GeneralMine/Wetterstation/Fritzing/Alles_Schaltplan.png

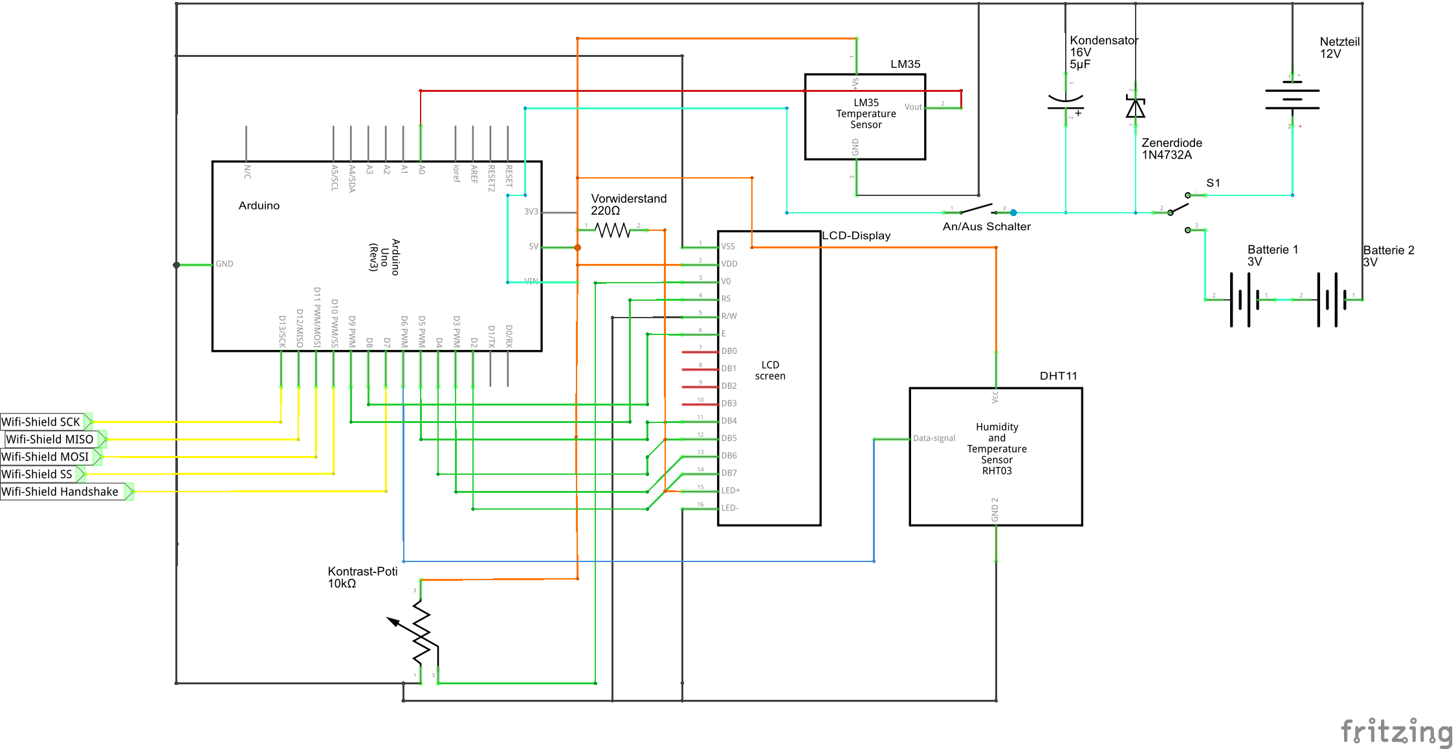
Fritzing/Alles_Schaltplan.png
