GeneralMine/Wetterstation/Medien/20160111_123831.jpg

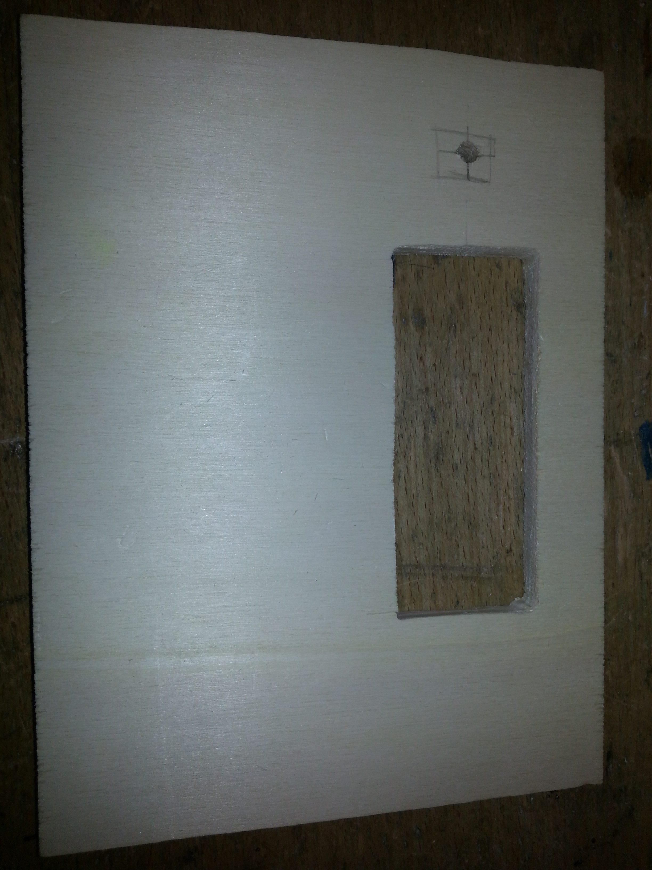
Medien/20160111_123831.jpg
