GeneralMine/Wetterstation/Medien/20160111_123935.jpg

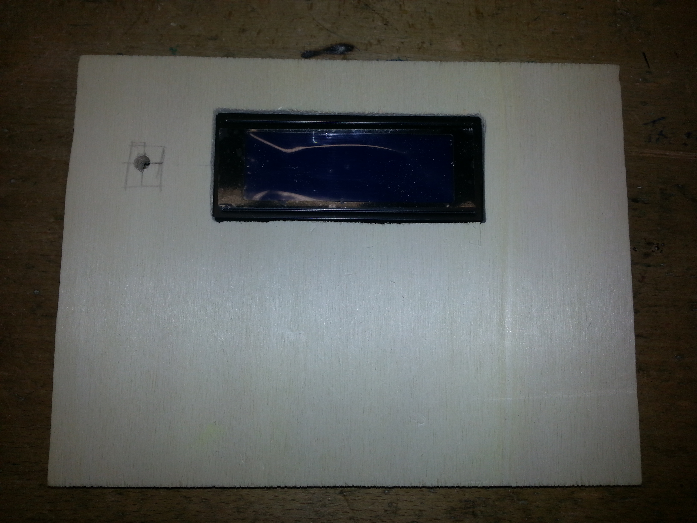
Medien/20160111_123935.jpg
