GeneralMine/Wetterstation/Medien/20160201_120405.jpg

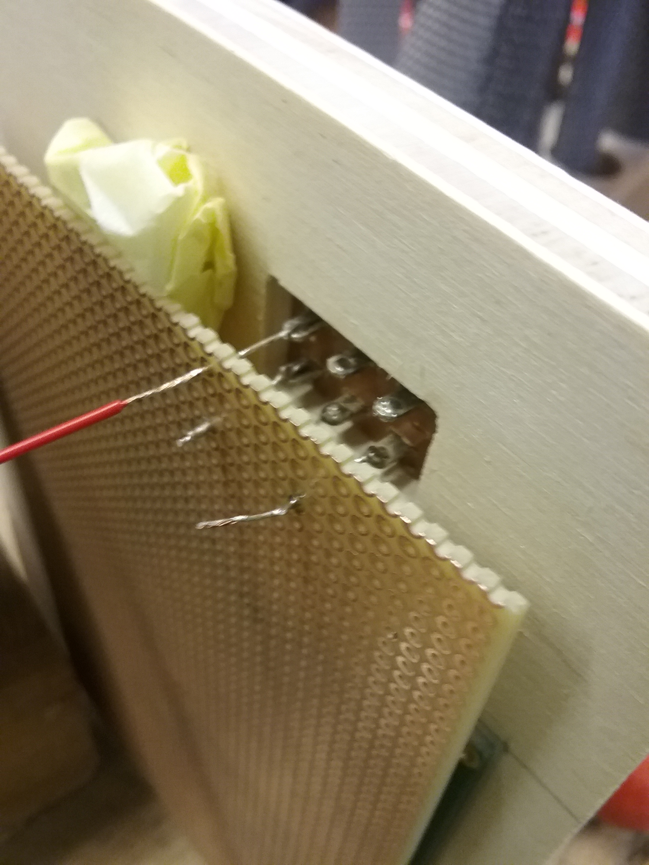
Medien/20160201_120405.jpg
