GeneralMine/Wetterstation/Medien/20160201_120416.jpg

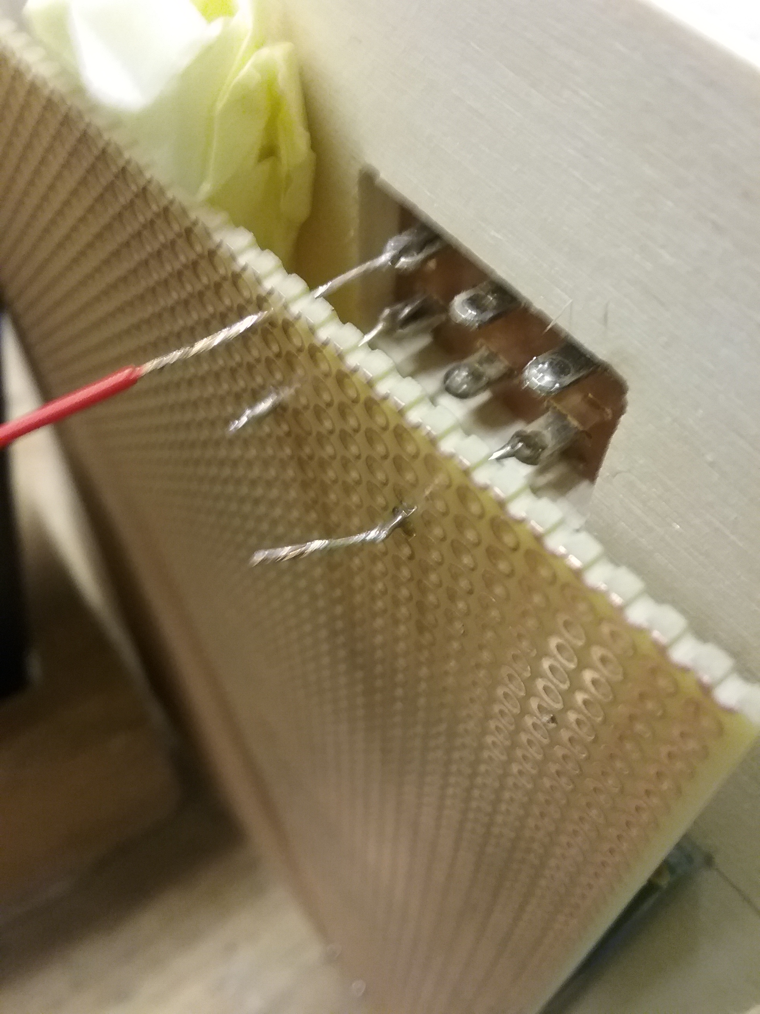
Medien/20160201_120416.jpg
