GeneralMine/Wetterstation/Medien/20160201_124902.jpg

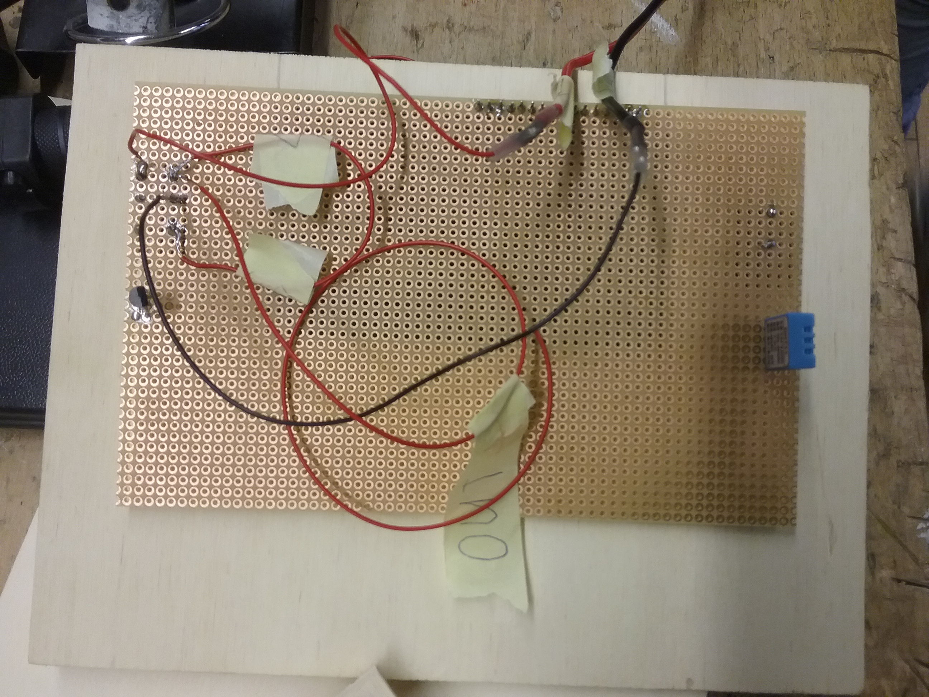
Medien/20160201_124902.jpg
