GeneralMine/Wetterstation/Medien/20160211_163818.jpg

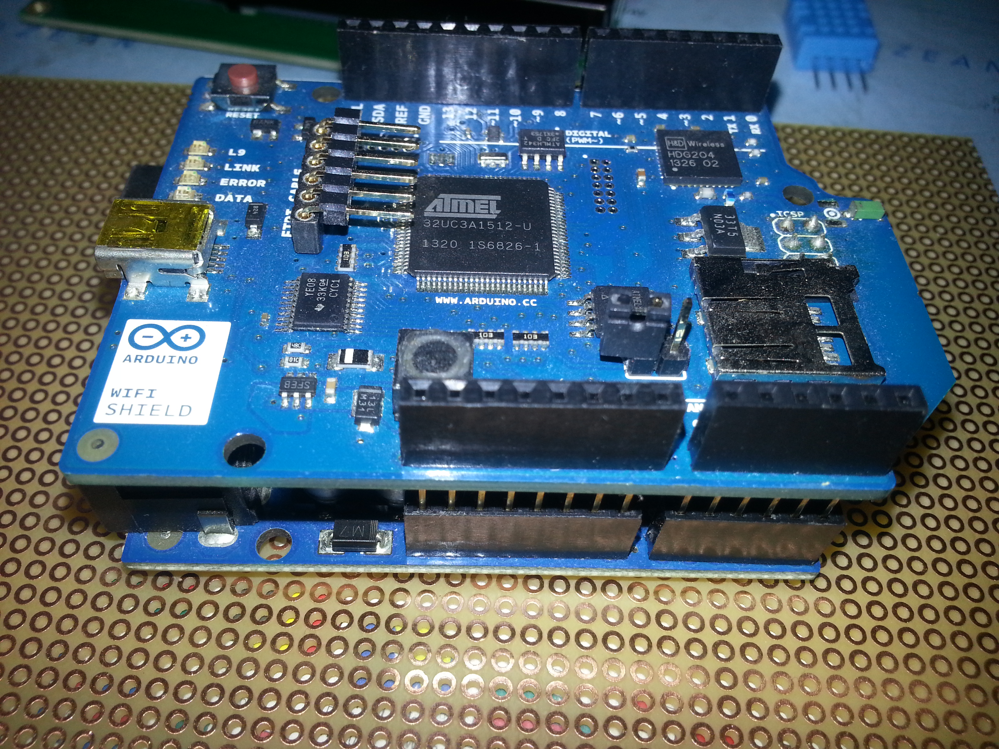
Medien/20160211_163818.jpg
