GeneralMine/Wetterstation/Medien/20160211_163850.jpg

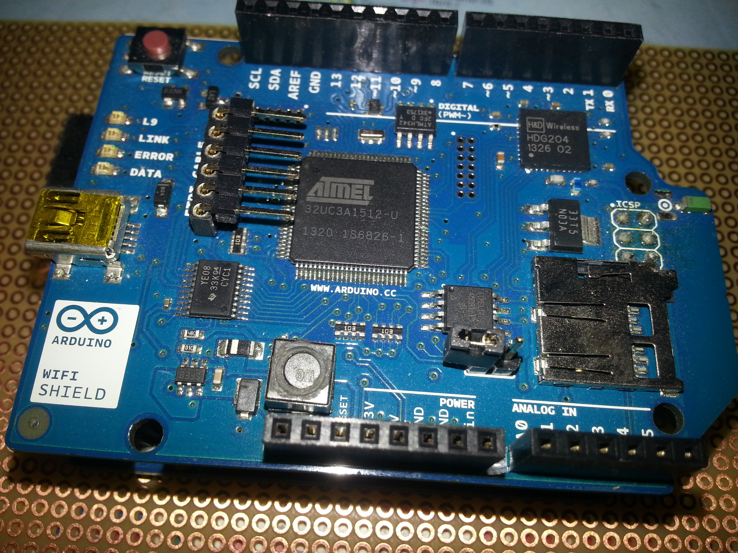
Medien/20160211_163850.jpg
