GeneralMine/Wetterstation/Medien/20160211_163903.jpg

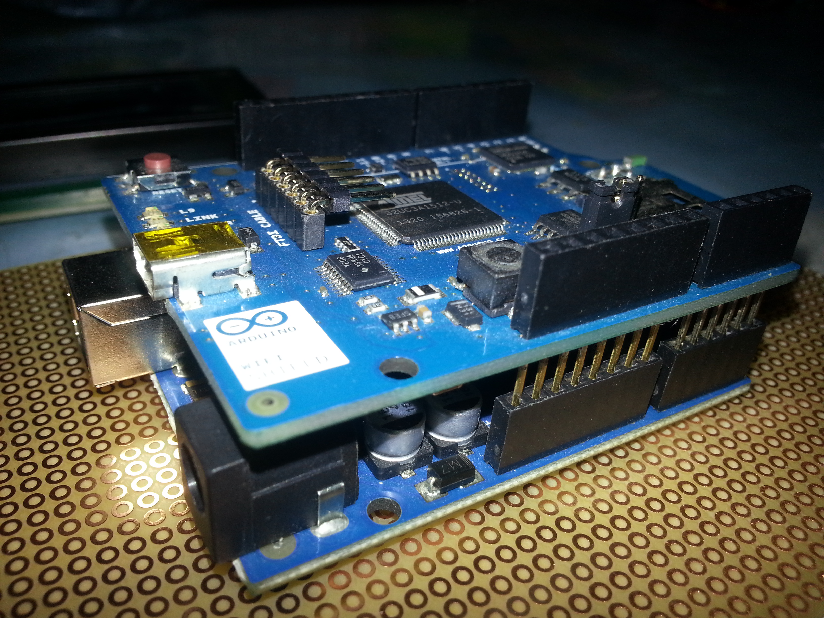
Medien/20160211_163903.jpg
