GeneralMine/Wetterstation/Medien/20160211_163923.jpg

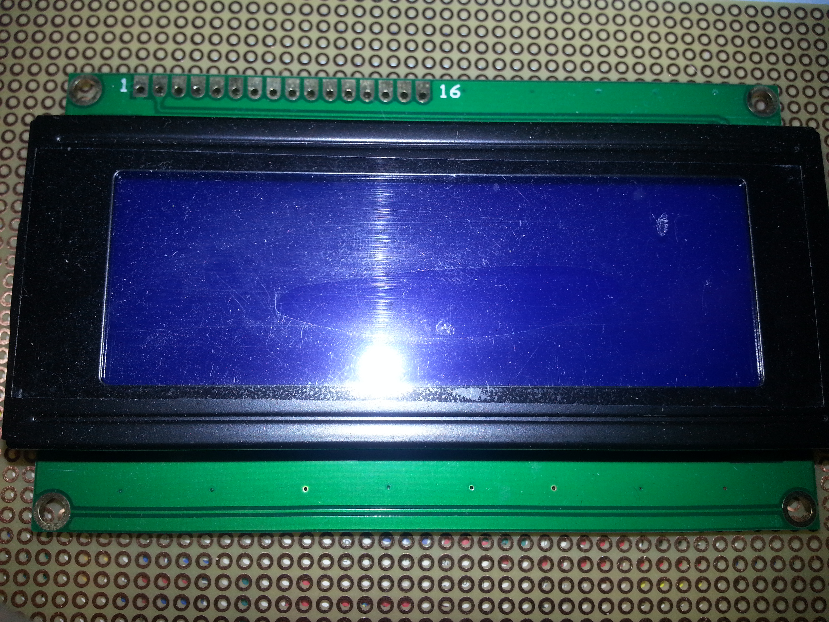
Medien/20160211_163923.jpg
