GeneralMine/Wetterstation/Medien/20160211_163938.jpg

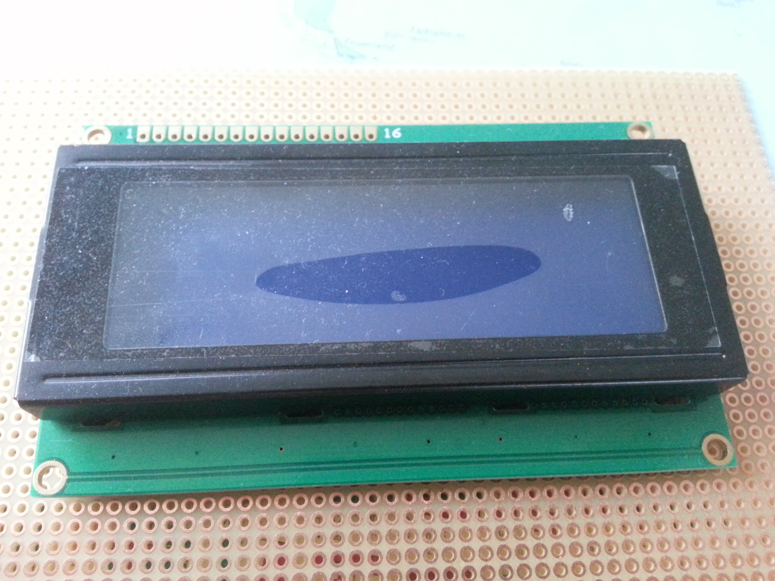
Medien/20160211_163938.jpg
