GeneralMine/Wetterstation/Medien/20160211_163947.jpg

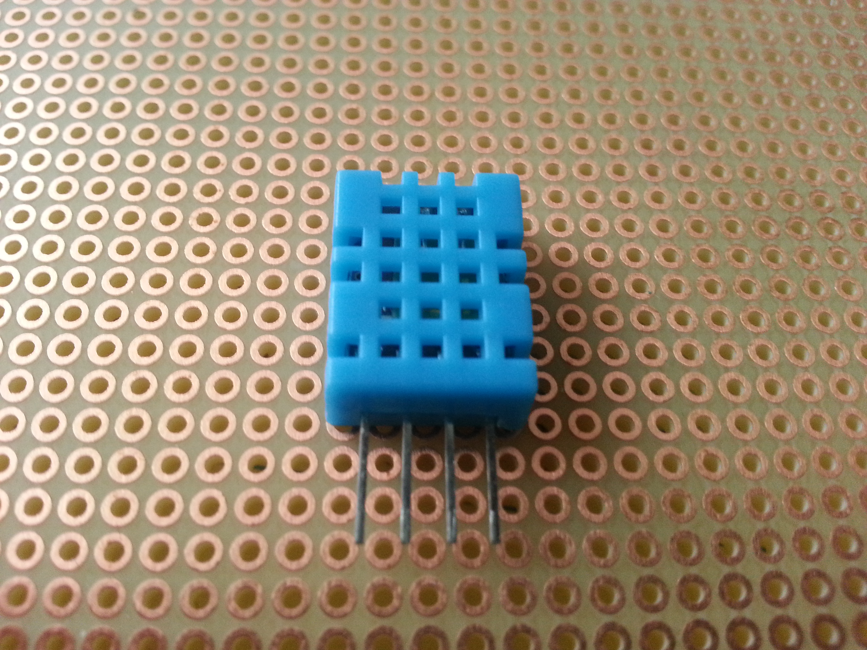
Medien/20160211_163947.jpg
