GeneralMine/Wetterstation/Medien/20160211_164001.jpg

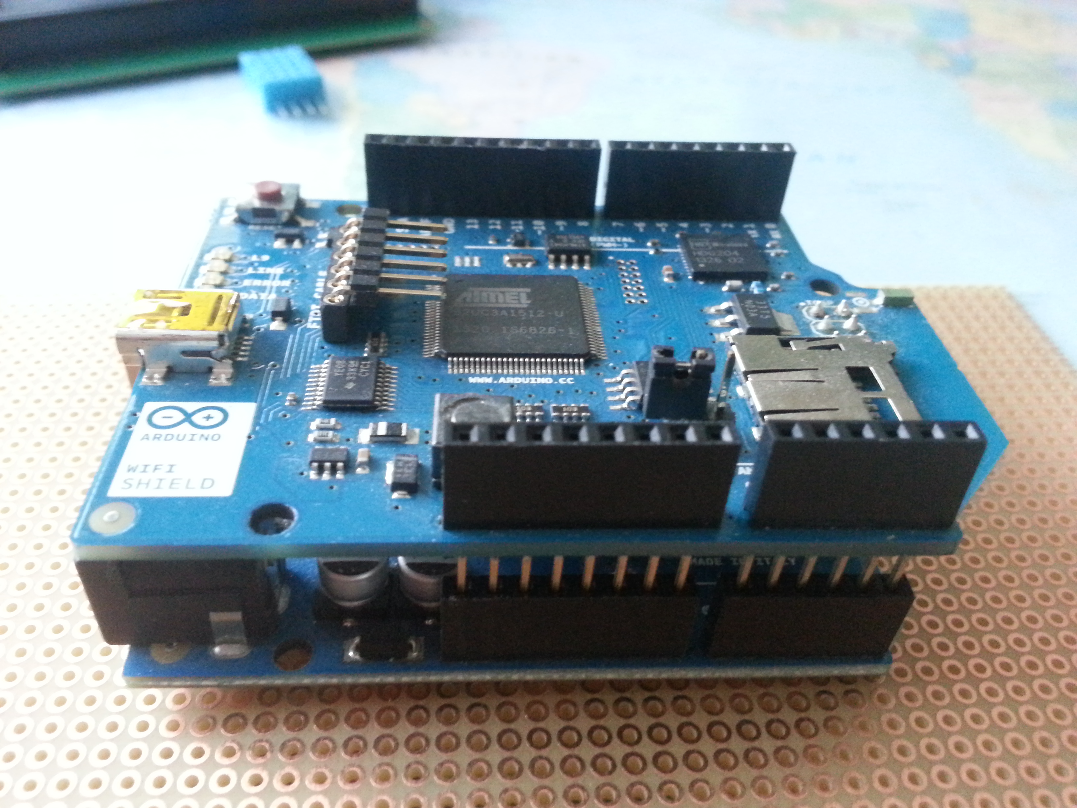
Medien/20160211_164001.jpg
