GeneralMine/Wetterstation/Medien/20160215_125352.jpg

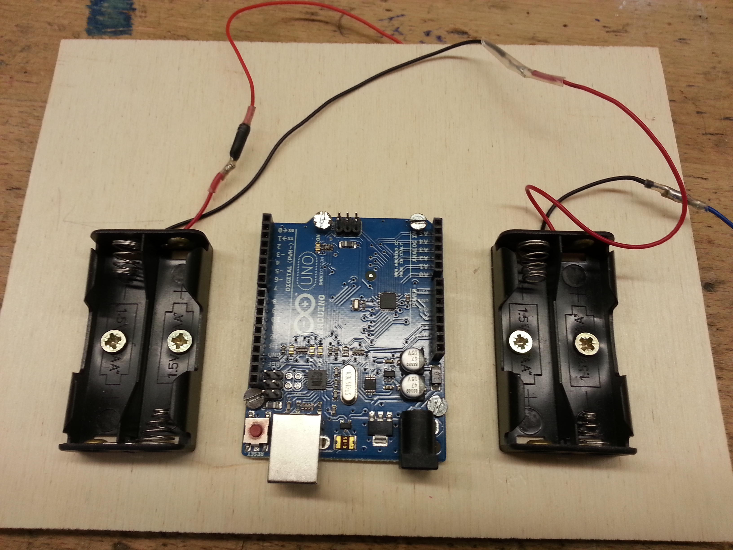
Medien/20160215_125352.jpg
