GeneralMine/Wetterstation/Medien/20160218_171619.jpg

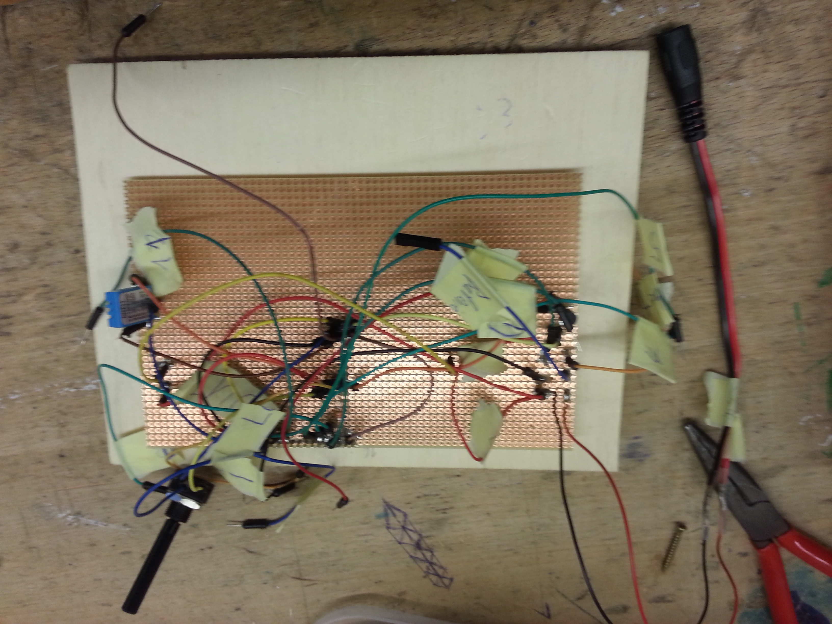
Medien/20160218_171619.jpg
