GeneralMine/Wetterstation/Medien/20160218_171622.jpg

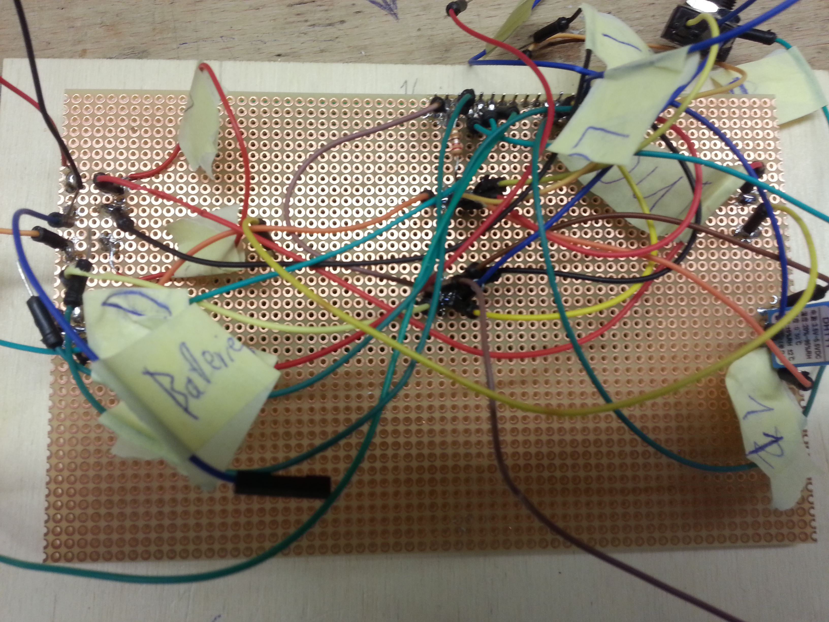
Medien/20160218_171622.jpg
