GeneralMine/Wetterstation/Medien/20160218_171625.jpg

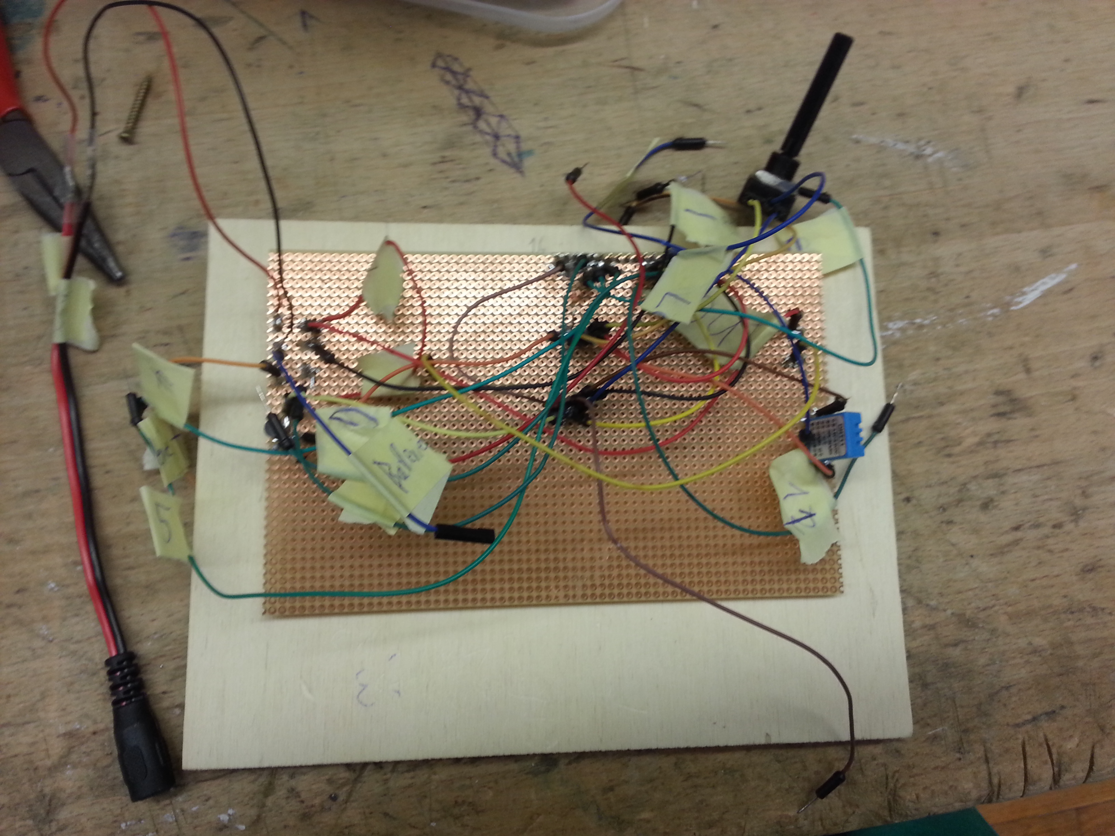
Medien/20160218_171625.jpg
