GeneralMine/Wetterstation/Medien/IMG-20151126-WA0028.jpg

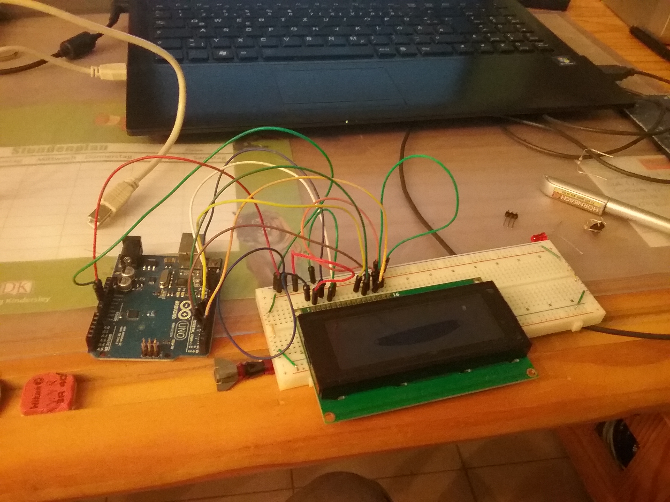
Medien/IMG-20151126-WA0028.jpg
