GeneralMine/Wetterstation/Medien/IMG-20151129-WA0023.jpg

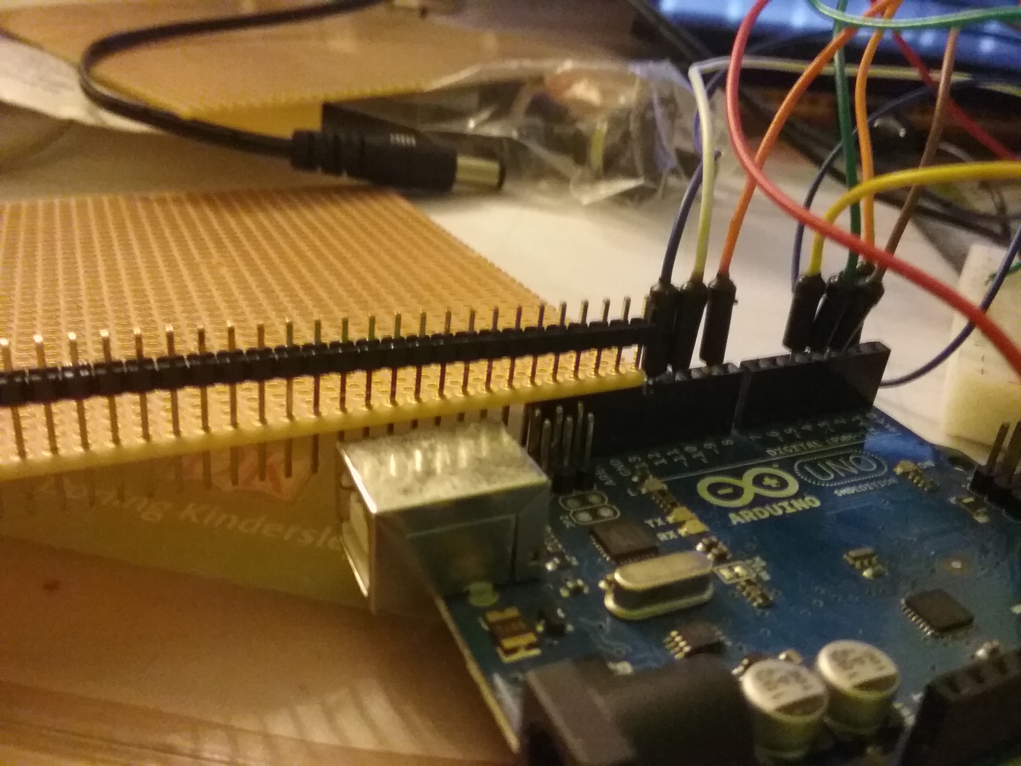
Medien/IMG-20151129-WA0023.jpg
