GeneralMine/Wetterstation/Medien/IMG-20151129-WA0031.jpg

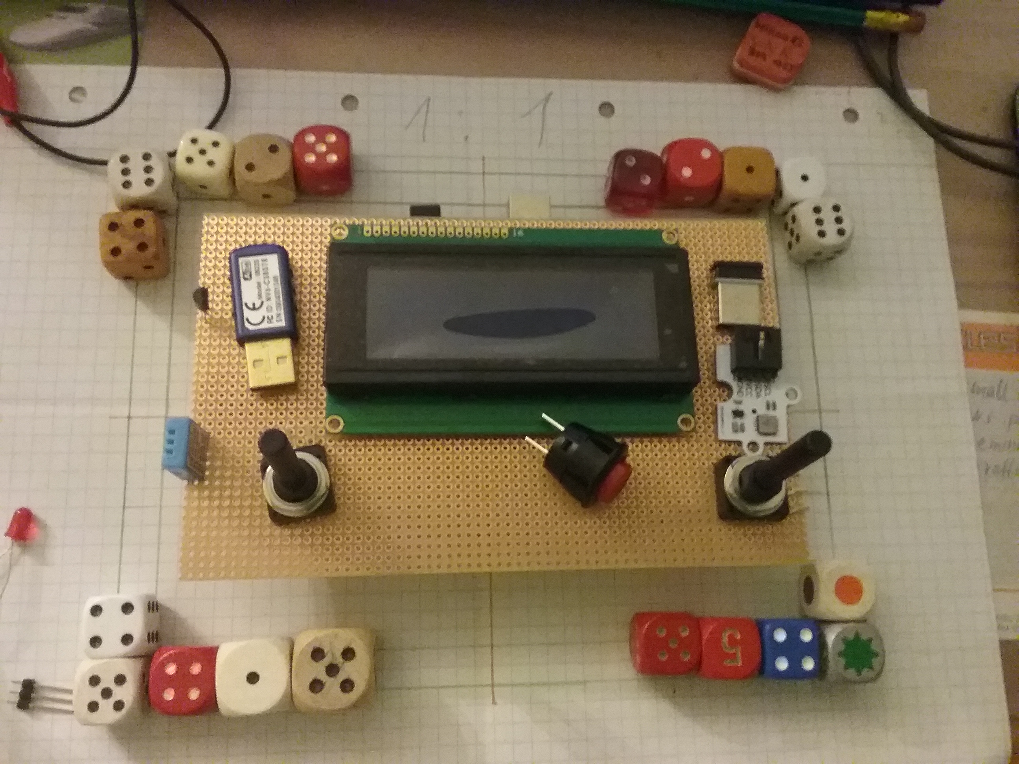
Medien/IMG-20151129-WA0031.jpg
