GeneralMine/Wetterstation/Medien/WS0001-4.png

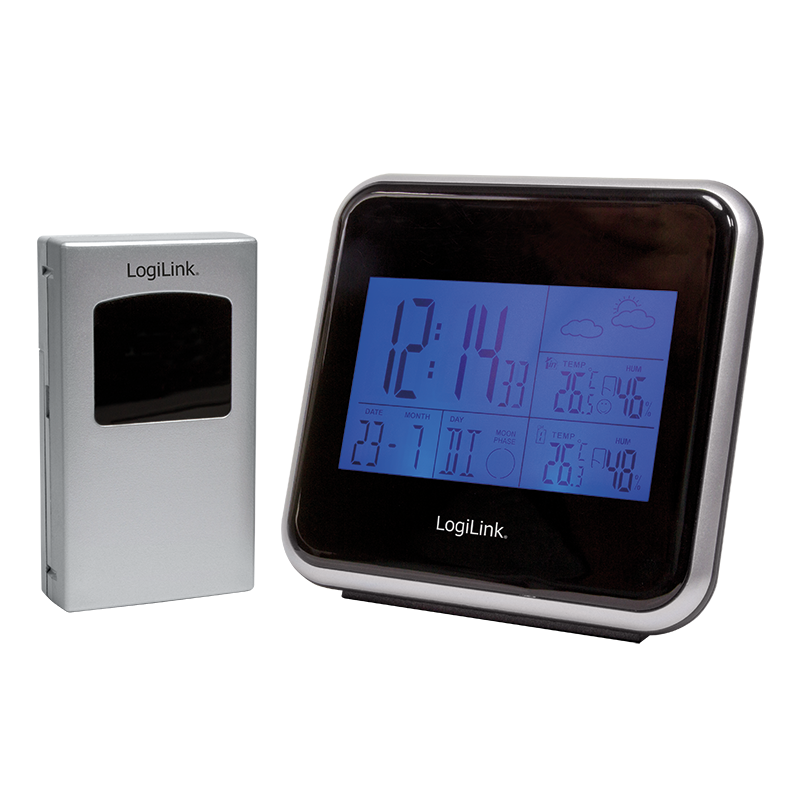
Medien/WS0001-4.png
