GeneralMine/Wetterstation/Planung/Screenshot_2015-12-08-23-06-10-1.png

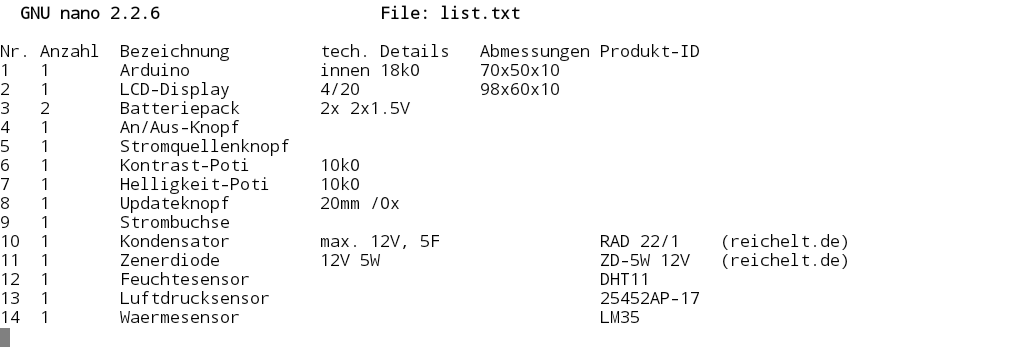
Planung/Screenshot_2015-12-08-23-06-10-1.png
