GeneralMine/Wetterstation/Planung/Screenshot_2015-12-08-23-07-43.png

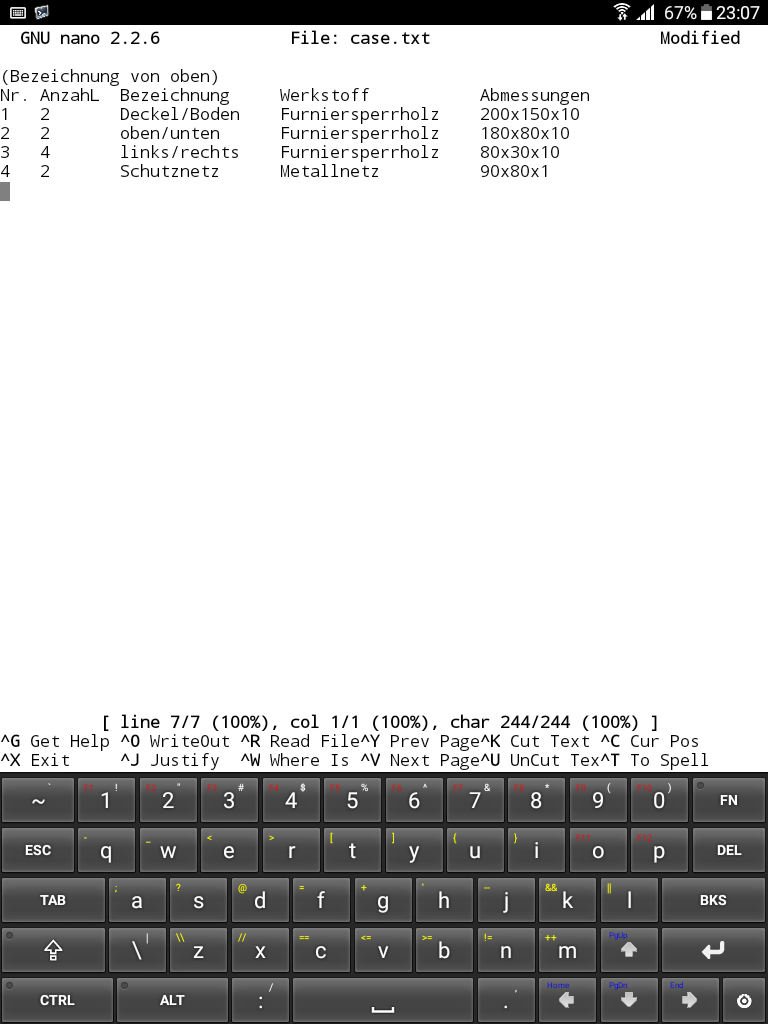
Planung/Screenshot_2015-12-08-23-07-43.png
