GeneralMine/Wetterstation/Planung/Stückliste2.png

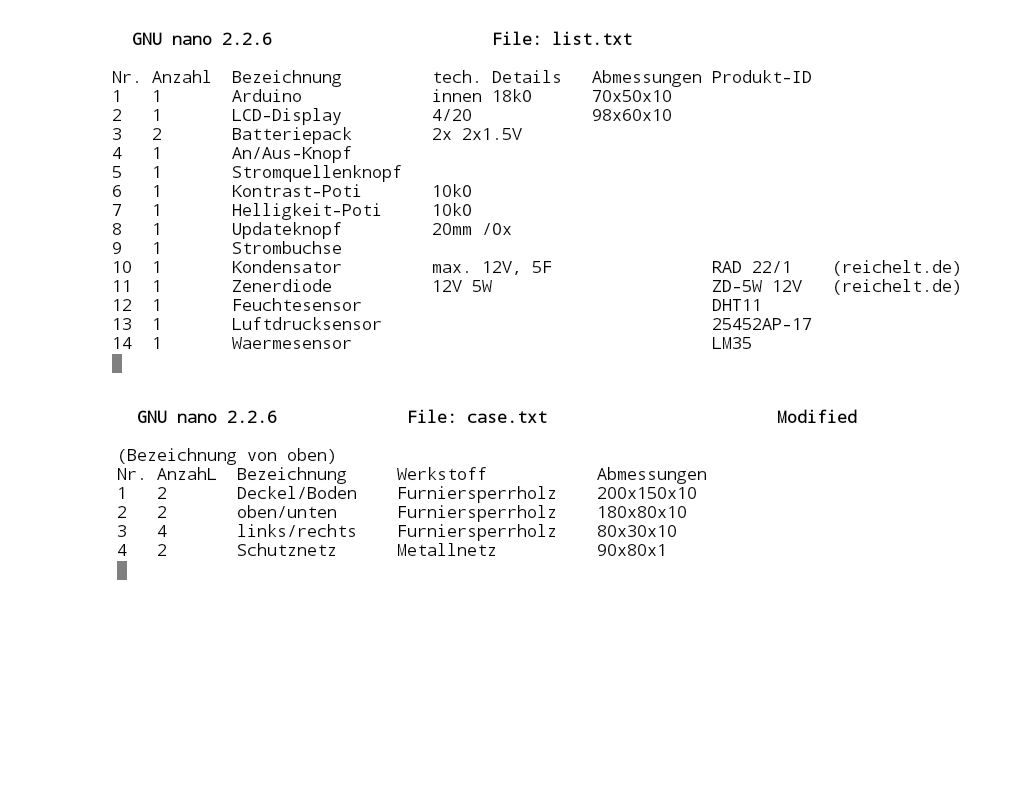
Planung/Stückliste2.png
